PStinno/micro-matrix-pcb/uMatrix_example/uMatrix_font.h

#ifndef _UMATRIX_FONT_H
#define _UMATRIX_FONT_H

uint8_t font[27][7] = {
  {0x1F, 0x11, 0x11, 0x1F, 0x11, 0x11, 0x11}, //A
  {0x1E, 0x11, 0x11, 0x1E, 0x11, 0x11, 0x1E}, //B
  {0x0E, 0x11, 0x10, 0x10, 0x10, 0x11, 0x0E}, //C
  {0x1E, 0x11, 0x11, 0x11, 0x11, 0x11, 0x1E}, //D
  {0x1E, 0x10, 0x10, 0x1E, 0x10, 0x10, 0x1E}, //E
  {0x1E, 0x10, 0x10, 0x1E, 0x10, 0x10, 0x10}, //F
  {0x0E, 0x11, 0x10, 0x10, 0x13, 0x11, 0x1E}, //G
  {0x11, 0x11, 0x11, 0x1F, 0x11, 0x11, 0x11}, //H
  {0x1F, 0x04, 0x04, 0x04, 0x04, 0x04, 0x1F}, //I
  {0x07, 0x02, 0x02, 0x02, 0x02, 0x0A, 0x0E}, //J
  {0x11, 0x12, 0x14, 0x18, 0x14, 0x12, 0x11}, //K
  {0x10, 0x10, 0x10, 0x10, 0x10, 0x10, 0x1F}, //L
  {0x11, 0x1B, 0x15, 0x15, 0x11, 0x11, 0x11}, //M
  {0x11, 0x11, 0x19, 0x15, 0x13, 0x11, 0x11}, //N
  {0x0E, 0x11, 0x11, 0x11, 0x11, 0x11, 0x0E}, //0
  {0x1E, 0x11, 0x11, 0x1E, 0x10, 0x10, 0x10}, //P
  {0x0E, 0x11, 0x11, 0x11, 0x11, 0x12, 0x0D}, //Q
  {0x1E, 0x11, 0x11, 0x1E, 0x14, 0x12, 0x11}, //R
  {0x1F, 0x10, 0x10, 0x1F, 0x01, 0x01, 0x1F}, //S
  {0x1F, 0x04, 0x04, 0x04, 0x04, 0x04, 0x04}, //T
  {0x11, 0x11, 0x11, 0x11, 0x11, 0x11, 0x1F}, //U
  {0x11, 0x11, 0x11, 0x11, 0x11, 0x0A, 0x04}, //V
  {0x11, 0x11, 0x11, 0x15, 0x15, 0x1B, 0x11}, //W
  {0x11, 0x11, 0x0A, 0x04, 0x0A, 0x11, 0x11}, //X
  {0x11, 0x11, 0x0A, 0x04, 0x04, 0x04, 0x04}, //Y
  {0x1F, 0x01, 0x02, 0x04, 0x08, 0x10, 0x1F}, //Z
  {0x00, 0x00, 0x00, 0x00, 0x00, 0x00, 0x00}  //[SPACE]
};

#endif
